barryshaffer/YAMA/images/IMG_0376.jpeg

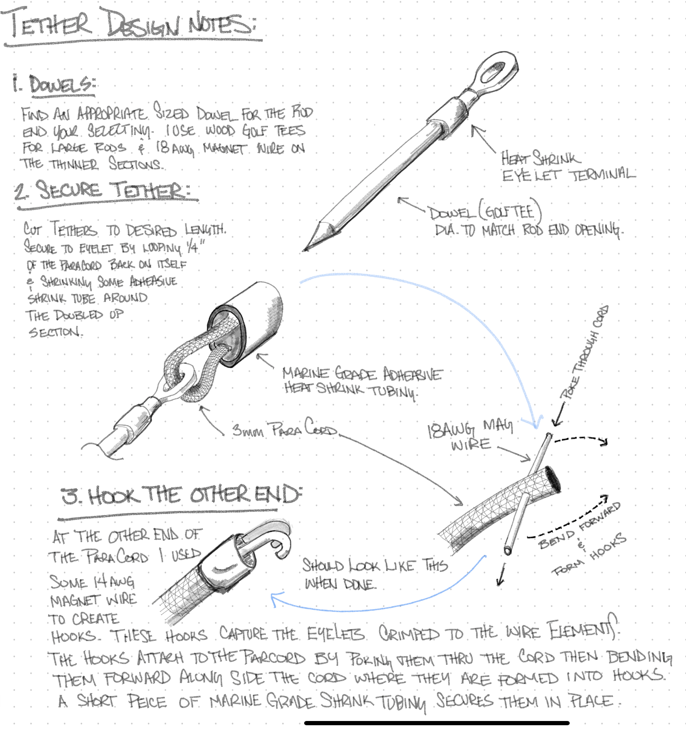
images/IMG_0376.jpeg
